ethanak/ESP32-suwmiarka/Suwmiarka/Lektor2.cpp

#include "lektor_private.h"
#include "Lektor2.h"
#include "audio.h"
#include "prefs.h"
#include <stdlib.h>
#include <string.h>
#include <ctype.h>

volatile bool isSpeaking;

Lektor2::Lektor2(void)
{
    //mSec_per_frame = 3.5;
    setTempo(pfs_tempo);
    //printf("\nPFS %f\n", mSec_per_frame);
    robotic = 0;
    g_samrate = 11050;
    g_f0_flutter = 0;
    setTempo(pfs_tempo);
    //g_nspfr = (g_samrate * mSec_per_frame) / 1000;
    frequency = 100;
    g_nfcascade = 6;
    mouth_callback = NULL;
    audioModule = nullptr;
    isSpeaking = 0;
#ifndef __linux__
    charcount = 0;
#endif
}

int Lektor2::setTempo(int s)
{
    if (s < 0 || s > 15) return -1;
    ctempo = s;
    mSec_per_frame = 10.0 - 0.5*s;
    g_nspfr = (g_samrate * mSec_per_frame) / 1000;

    return 0;
}
int Lektor2::setSpeed(float s)
{
    if (s < -1.0 || s > 1.0) return LEKTOR_ERROR_ILLEGAL;
    mSec_per_frame = 8.0 - 2.0 * s;
    g_nspfr = (g_samrate * mSec_per_frame) / 1000;

    return 0;
}

int Lektor2::setRobotic(int n)
{
    robotic = n ? 1 : 0;
    return 0;
}

int Lektor2::setFrequency(int t)
{
    if (t < 60 || t > 400) return LEKTOR_ERROR_ILLEGAL;
    frequency = t;
    return 0;
}

int Lektor2::setSampleFreq(int t)
{
    if (t < 8000 || t > 16000) return LEKTOR_ERROR_ILLEGAL;
    g_samrate = t;
    g_nspfr = (g_samrate * mSec_per_frame) / 1000;
    return 0;
}


void Lektor2::setMouthCallback(void (*callback)(int))
{
    mouth_callback = callback;
}

int Lektor2::say(const char *str)
{
    strcpy(buffer, str);
    return say_buffer();
}

int Lektor2::say_buffer(void)
{
    int rc=0;
    isSpeaking=1;
    char *strp;
    rc = toISO2(buffer, sizeof(buffer));
    if (rc) return rc;
    strp = buffer;
    setTempo(pfs_tempo);
    //printf("PMS %f\n", mSec_per_frame); 
    g_nspfr = (g_samrate * mSec_per_frame) / 1000;
    if (audioModule) audioModule->init_audio();
    else return LEKTOR_ERROR_NOT_COMPLETE;
    for (;;) {
        rc= getPhrase(buffer, LEKTOR_BUFFER_SIZE, &strp);
        if (rc < 0) break;
#if DEBUG
        printf("Mode = %d, boundary = %d\n",
            rc & 7, rc >> 3);
#endif
        rc = holmes((uint16_t *)buffer, rc);
        if (rc) break;
    }
    audioModule -> finalize_audio();
#ifndef __linux__
    charcount = 0;
#endif
    isSpeaking = 0;
    return rc;
}

#ifndef __linux__

size_t Lektor2::wwrite(uint16_t znak)
{
    if (znak < 0x80) return write(znak);
    if (znak < 0x800) {
        if (!write((znak >> 6) | 0xc0)) return 0;
        return write((znak & 0x3f) | 0x80)?2:0;
    }
    if (!write((znak >> 12) | 0xe0)) return 0;
    if (!write(((znak >> 6) & 0x3f) | 0x80)) return 0;
    return write((znak & 0x3f) | 0x80)?3:0;
}


size_t Lektor2::write(uint8_t znak)
{
    if (znak != '\n') {
        if (charcount >= LEKTOR_BUFFER_SIZE - 2) {
            return 0;
        }
        buffer[charcount++]=znak;
        return (size_t)1;
    }
    buffer[charcount] = 0;
    if (charcount) {
        clean();
        if ((last_error = say_buffer())) {
            return 0;
        }
    }
    return (size_t)1;
}

void Lektor2::clean(void)
{
    charcount = 0;
    last_error = 0;
}

void Lektor2::flush(void)
{
    buffer[charcount] = 0;
    say_buffer();
}

int Lektor2::printf(const char *format, ...)
{
    char print_buf[LEKTOR_PRINTF_SIZE];
    int cnt, i;
    va_list ap;
    va_start(ap, format);
    cnt = vsnprintf(print_buf, LEKTOR_PRINTF_SIZE, format, ap);
    va_end(ap);
    if (cnt > LEKTOR_PRINTF_SIZE) {
        cnt = LEKTOR_PRINTF_SIZE;
    }
    for (i = 0; i < cnt; i++) {
        if (!write((uint8_t)print_buf[i])) {
            return last_error;
        }
    }
    return 0;
}

#ifdef F
int Lektor2::printf(const __FlashStringHelper *format, ...)
{
    char print_buf[LEKTOR_PRINTF_SIZE];
    int cnt, i;
    va_list ap;
    va_start(ap, format);
#ifdef __AVR__
    cnt = vsnprintf_P(print_buf, LEKTOR_PRINTF_SIZE, (const char *)format, ap);
#else
    cnt = vsnprintf(print_buf, LEKTOR_PRINTF_SIZE, (const char *)format, ap);
#endif
    va_end(ap);
    if (cnt > LEKTOR_PRINTF_SIZE) {
        cnt = LEKTOR_PRINTF_SIZE;
    }
    for (i = 0; i < cnt; i++) {
        if (!write((uint8_t)print_buf[i])) {
            return last_error;
        }
    }
    return 0;
}

void Lektor2::beep(int freq)
{
    if (audioModule) audioModule->beep(freq);
}
#endif
#endif
